caiannello/Pugputer6309/3D_Models/backplane_bot.png

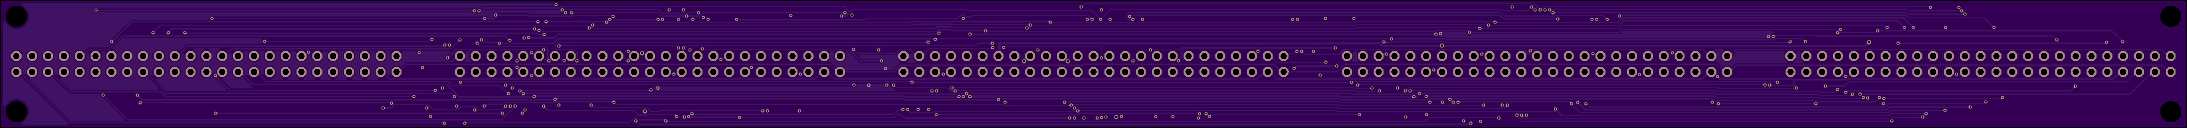
3D_Models/backplane_bot.png
