caiannello/Pugputer6309/3D_Models/backplane_top.png

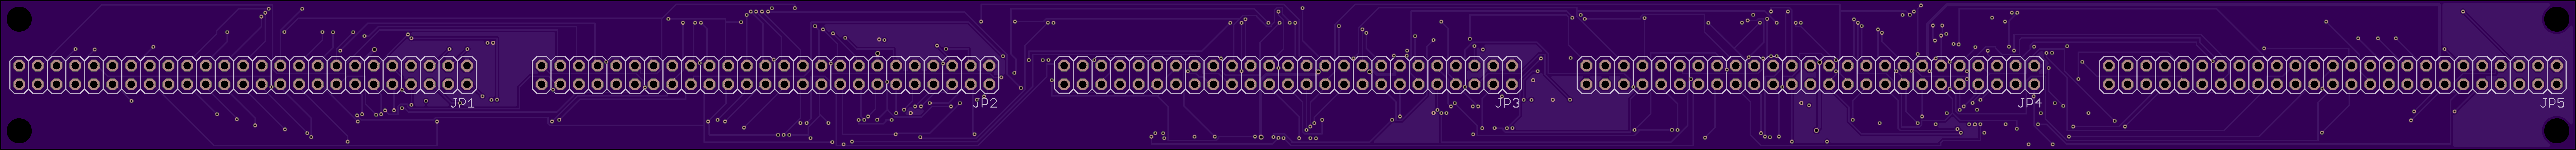
3D_Models/backplane_top.png
