caiannello/Pugputer6309/3D_Models/c_cpu_bot.png

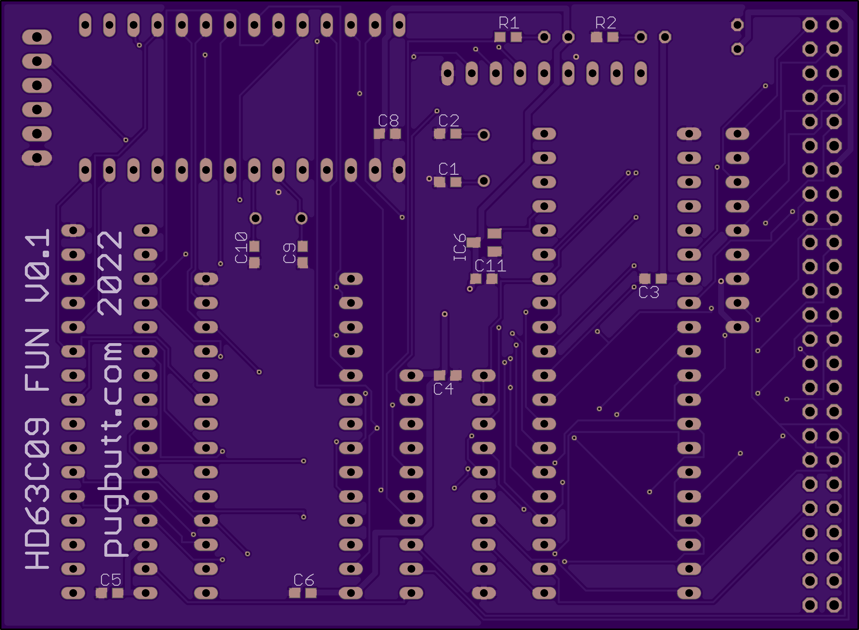
3D_Models/c_cpu_bot.png
