caiannello/Pugputer6309/3D_Models/c_cpu_top.png

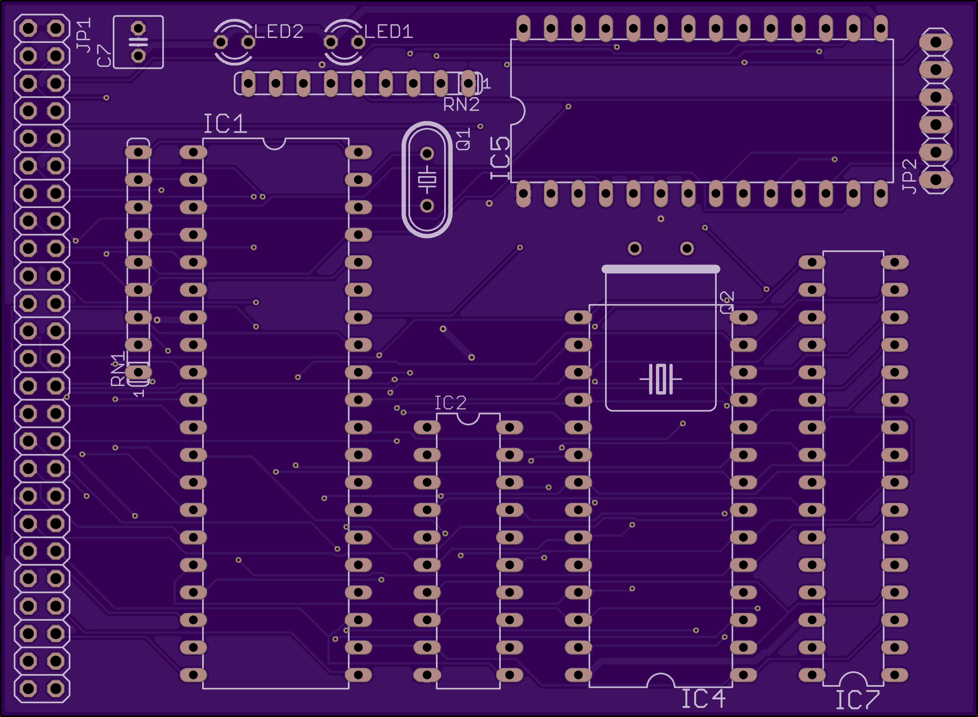
3D_Models/c_cpu_top.png
