caiannello/Pugputer6309/3D_Models/kb.jpg

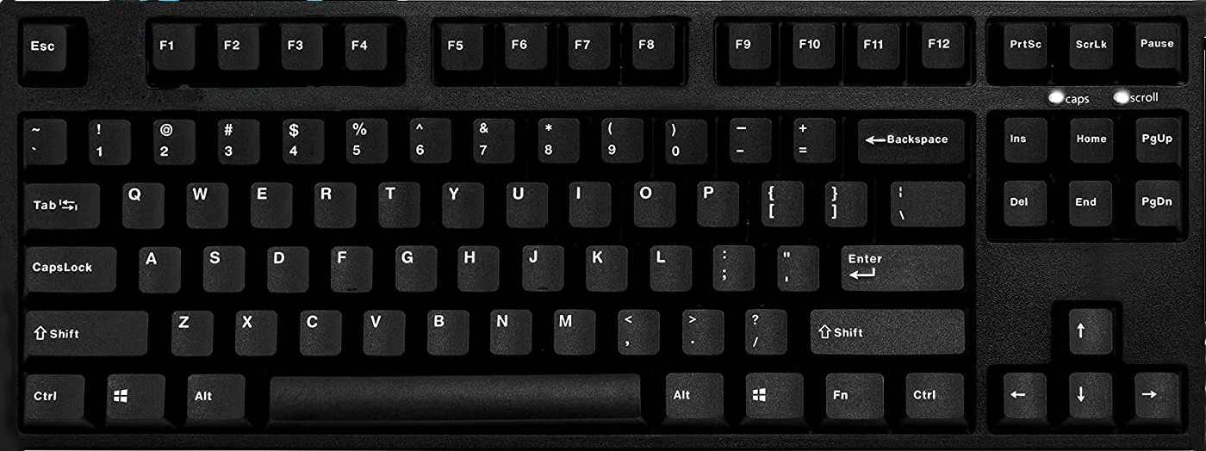
3D_Models/kb.jpg
