caiannello/Pugputer6309/3D_Models/lv_parallel_bot.png

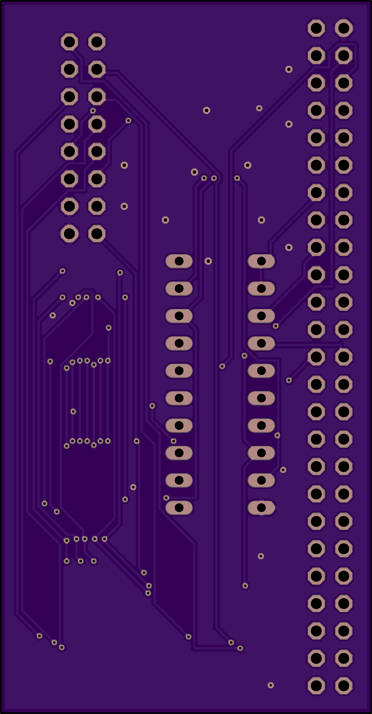
3D_Models/lv_parallel_bot.png
