caiannello/Pugputer6309/3D_Models/lv_parallel_top.png

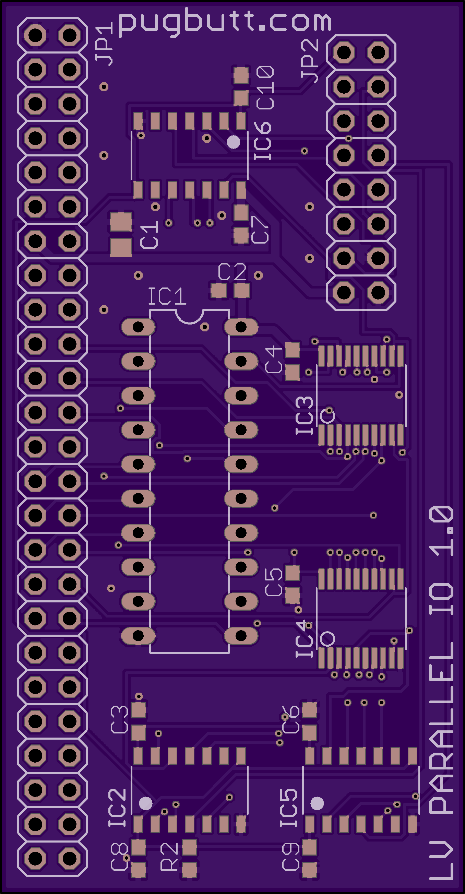
3D_Models/lv_parallel_top.png
