caiannello/Pugputer6309/3D_Models/mega_multi_bot.png

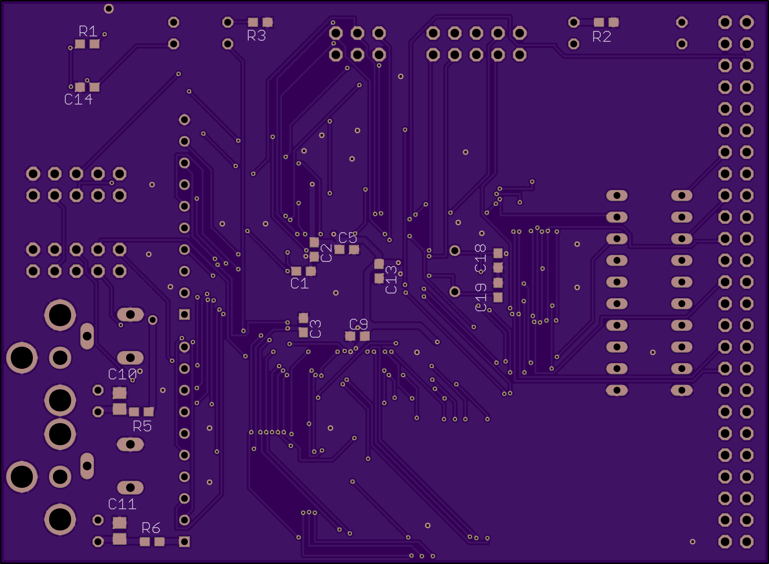
3D_Models/mega_multi_bot.png
