caiannello/Pugputer6309/3D_Models/mega_multi_top.png

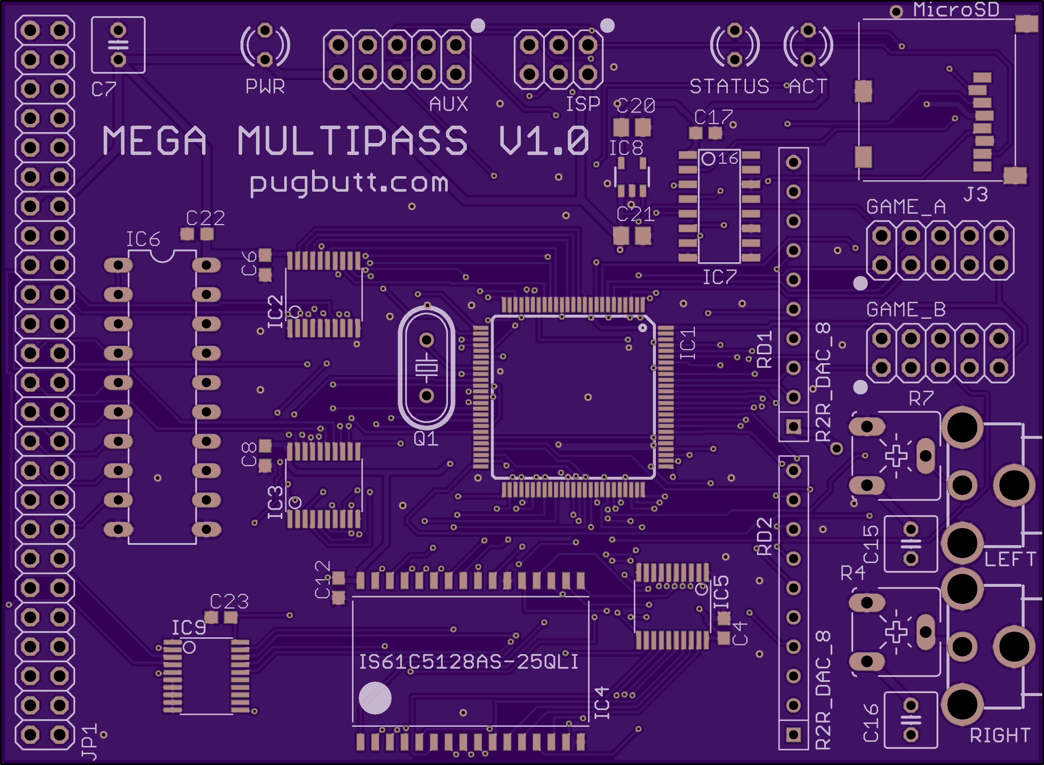
3D_Models/mega_multi_top.png
