caiannello/Pugputer6309/3D_Models/v9958_video_top.png

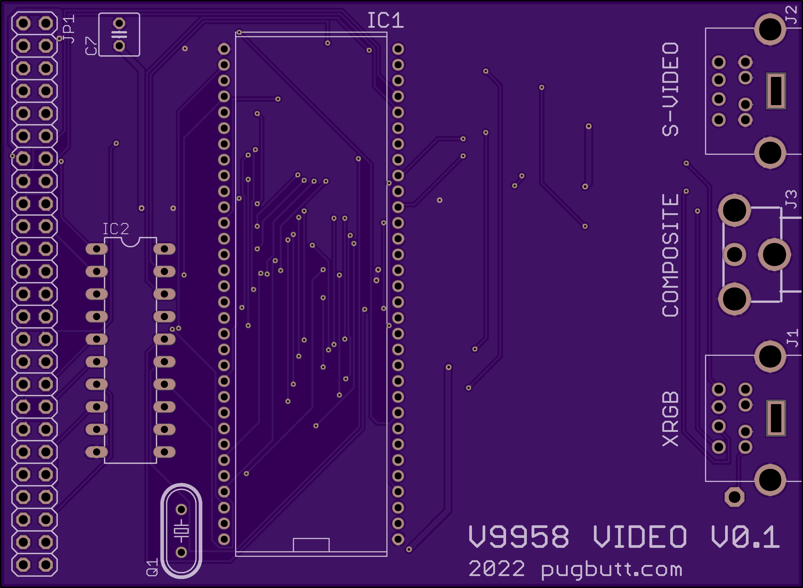
3D_Models/v9958_video_top.png
