caiannello/Pugputer6309/3D_Models/wedge_kb_top.png

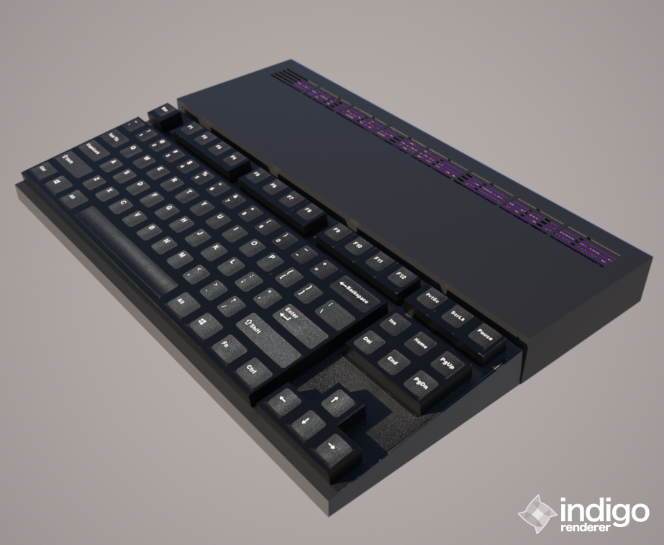
3D_Models/wedge_kb_top.png
