caiannello/Pugputer6309/Hardware/Bus Breakout Card/Layout.png

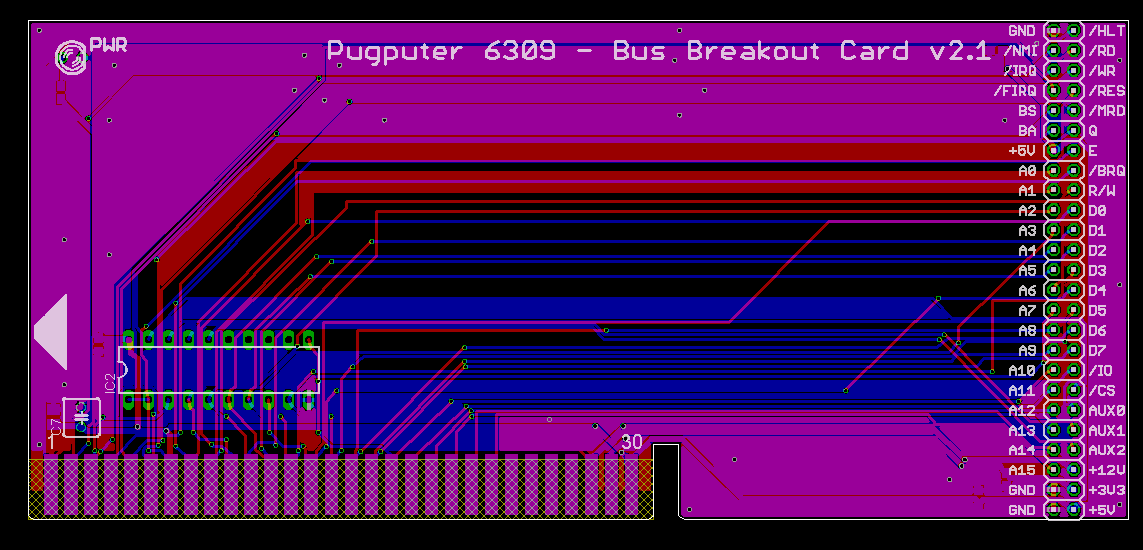
Hardware/Bus Breakout Card/Layout.png
