caiannello/Pugputer6309/Hardware/Bus Breakout Card/Schematic.png

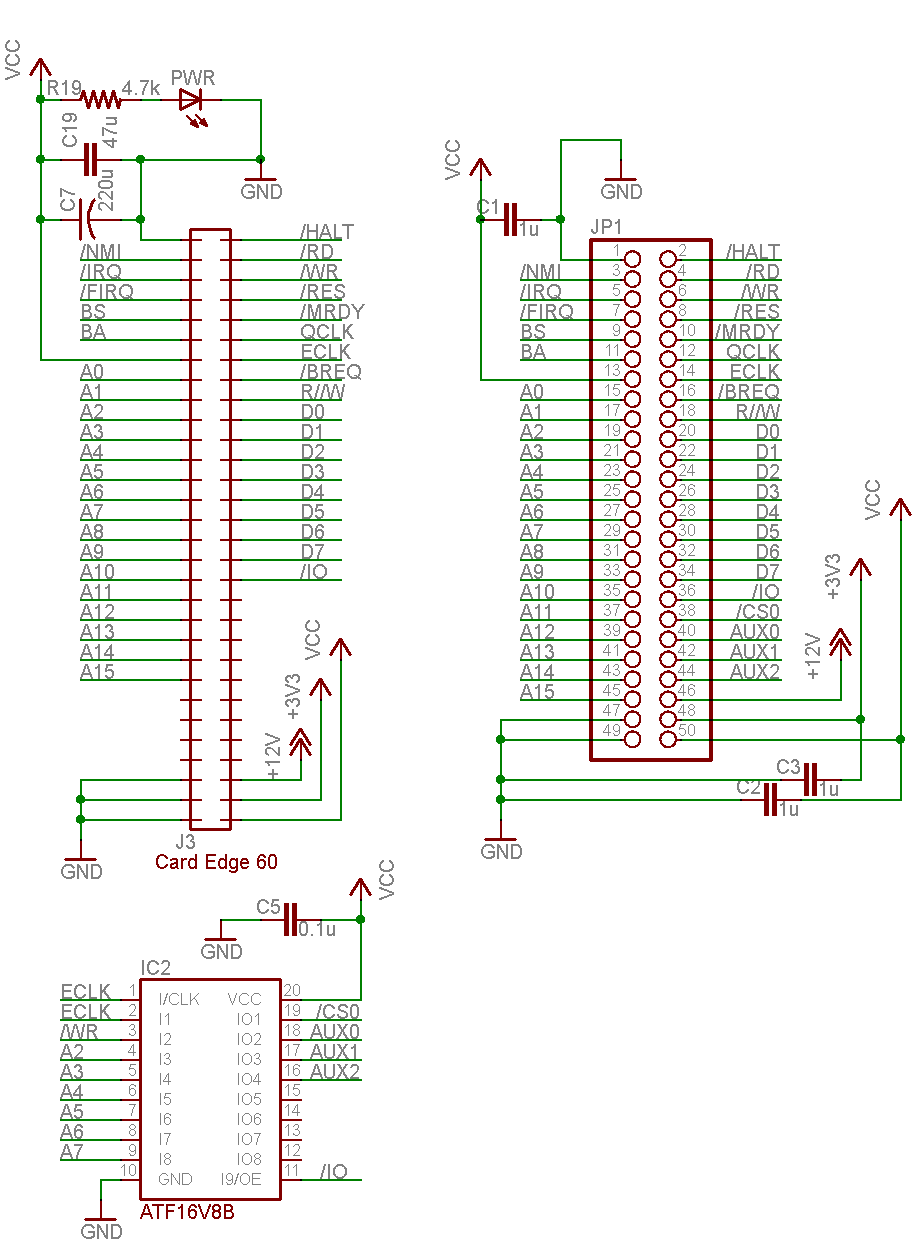
Hardware/Bus Breakout Card/Schematic.png
