caiannello/Pugputer6309/Hardware/Parallel IO Card/Parallel IO Card Schematic.png

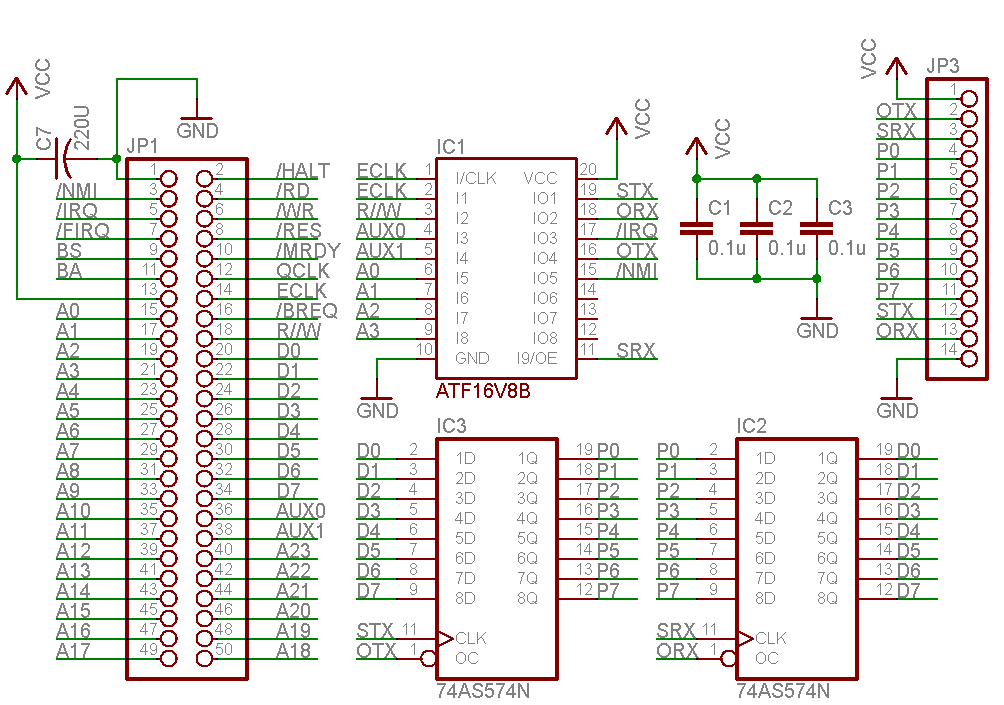
Hardware/Parallel IO Card/Parallel IO Card Schematic.png
