caiannello/Pugputer6309/Hardware/Pico_WLAN_SD_USB_RTC_AUDIO/layout.png

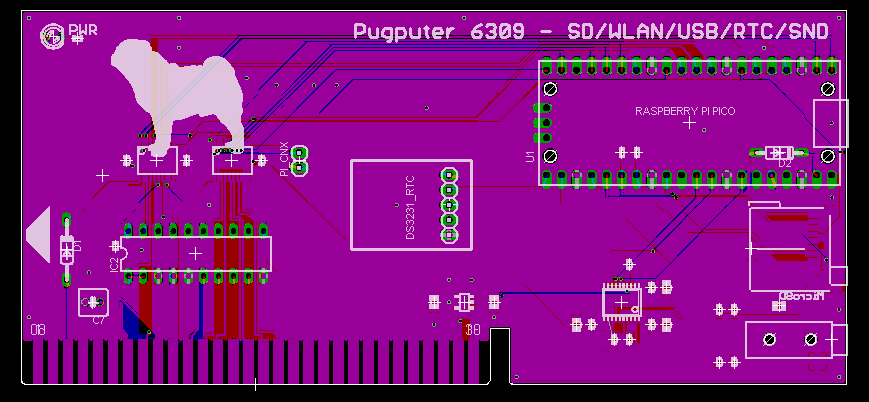
Hardware/Pico_WLAN_SD_USB_RTC_AUDIO/layout.png
