caiannello/Pugputer6309/Hardware/V9958 Video Card/past_revs/V9958 Video Card Schematic.png

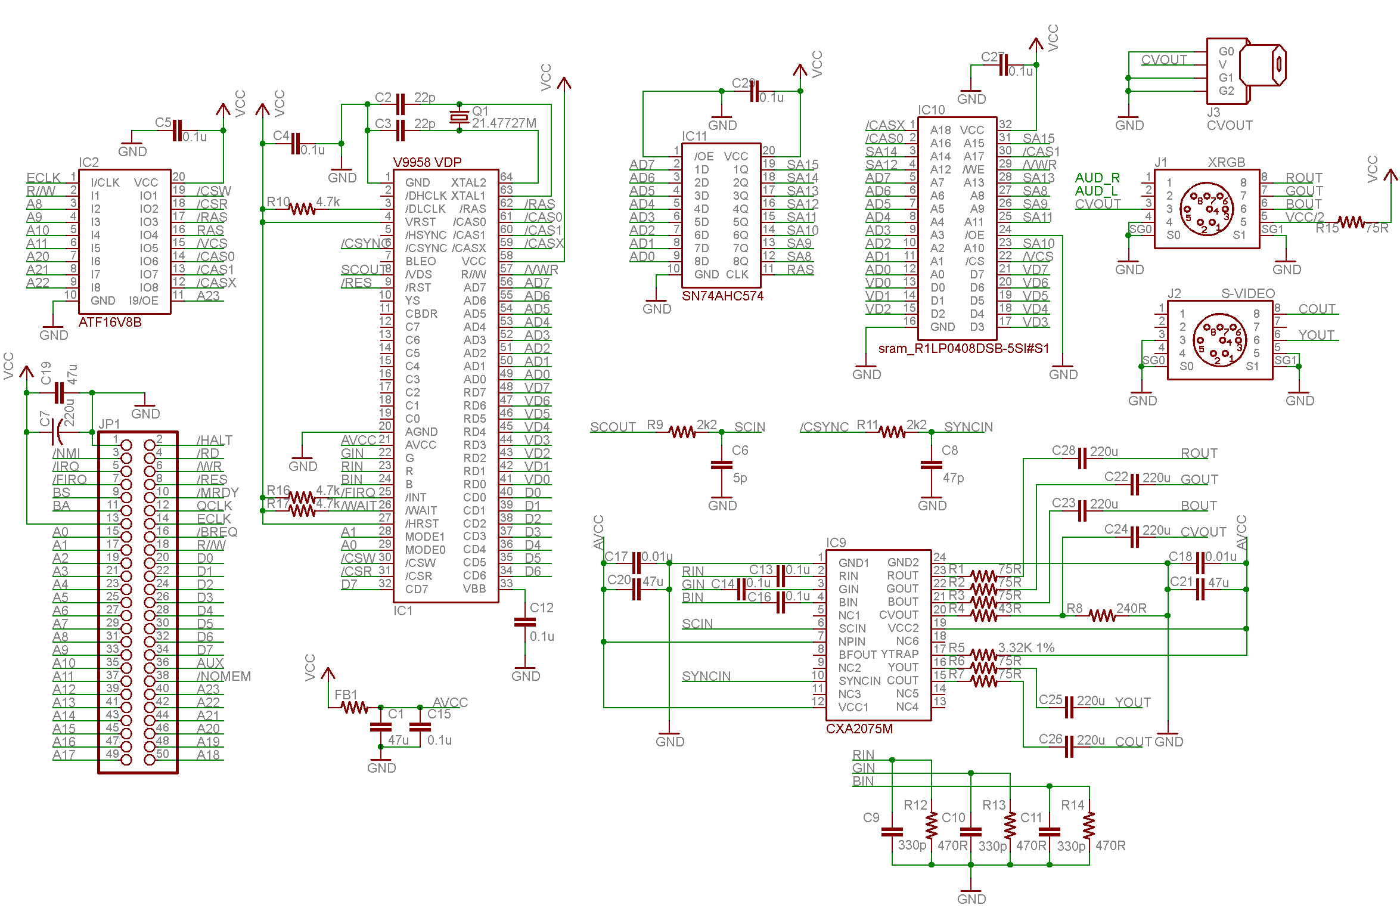
Hardware/V9958 Video Card/past_revs/V9958 Video Card Schematic.png
