caiannello/Pugputer6309/Software/dev_utils/font_palette.png

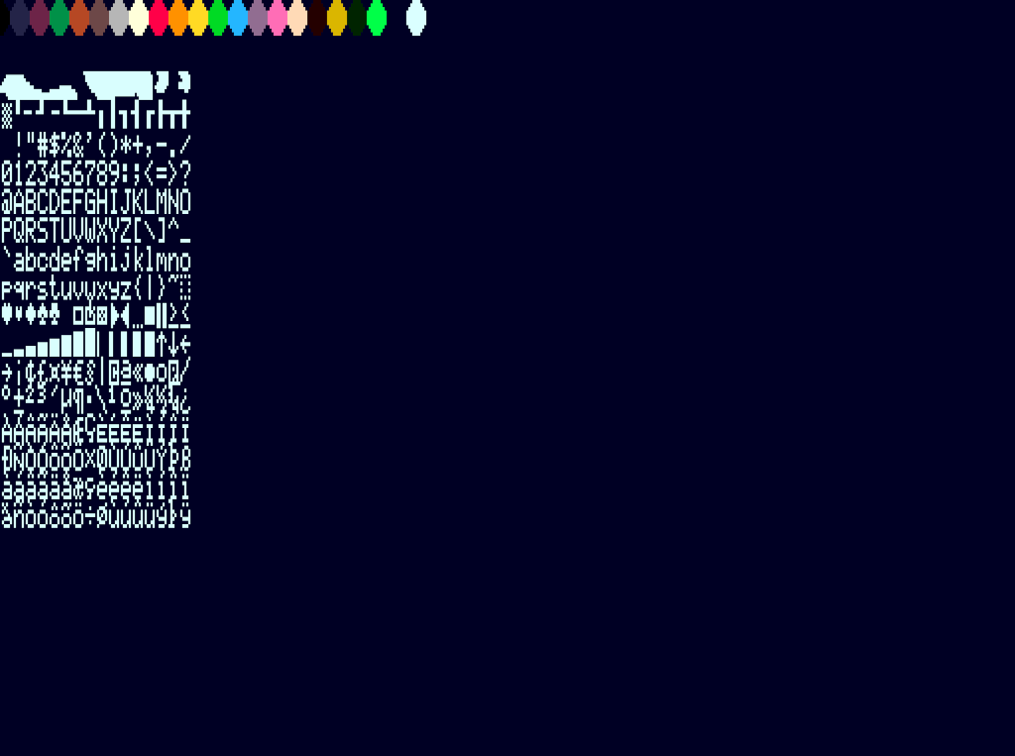
Software/dev_utils/font_palette.png
