caiannello/Pugputer6309/Software/dev_utils/font_palette/24bit_parrot.png

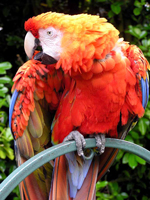
Software/dev_utils/font_palette/24bit_parrot.png
