caiannello/Pugputer6309/Hardware/6309 CPU Card/experimental/README.md

## 6309 CPU Card v2 through-hole experiment
```
Same as the Rev v2 in the parent directory, except most IC's are using
through-hole packages. (Had to give up one of the 512KB SRAM's to make room.)
```
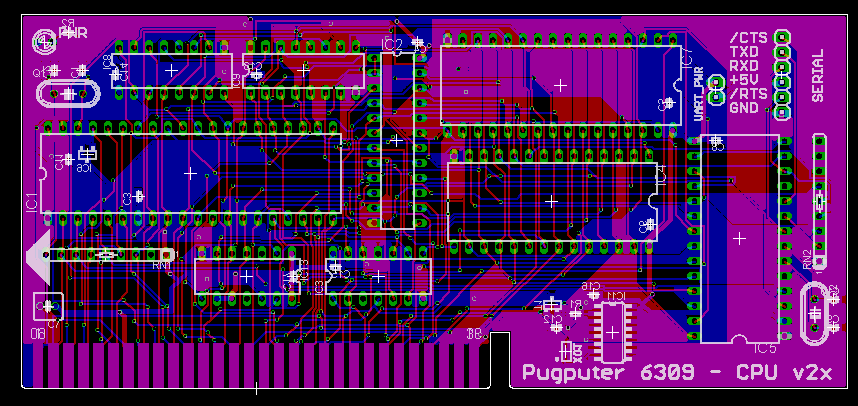
[picture p64: Hardware/6309 CPU Card/experimental/layout.png]
layout


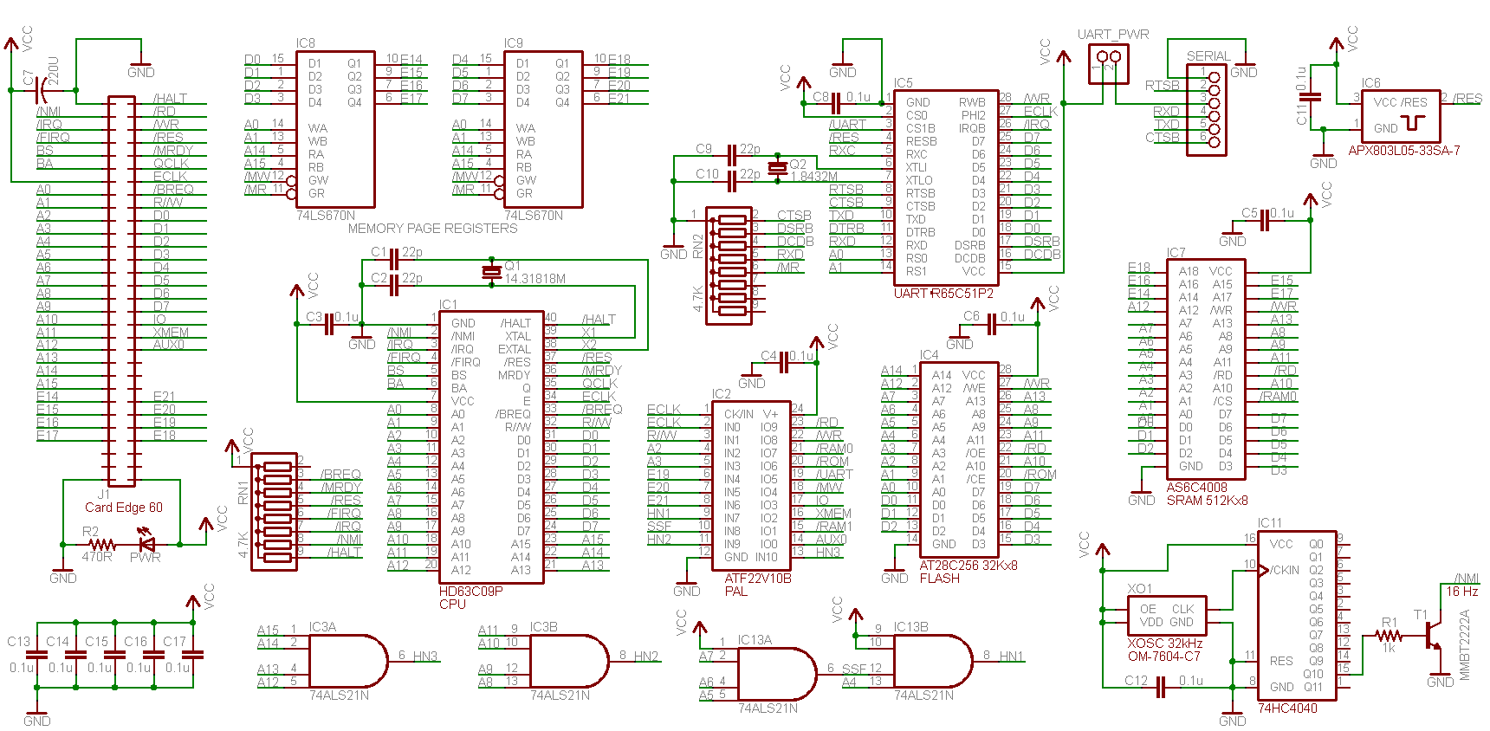
[picture p65: Hardware/6309 CPU Card/experimental/schematic.png]
schematic
