caiannello/Pugputer6309/Software/Arduino UNO/parallel_sd_audio/sd.h

///////////////////////////////////////////////////////////////////////////////
///////////////////////////////////////////////////////////////////////////////
#ifndef __SD_H__
#define __SD_H__

void sd_init(void);
void sd_service(void);

void sd_send_dir(uint8_t *path = NULL);
void sd_send_file(char * filepath);

#endif
///////////////////////////////////////////////////////////////////////////////
///////////////////////////////////////////////////////////////////////////////
