caiannello/Pugputer6309/Software/Teensy 4.1/multipass/audio.h

// ----------------------------------------------------------------------------
// ----------------------------------------------------------------------------
#ifndef __AUDIO_H__
#define __AUDIO_H__
// ----------------------------------------------------------------------------
#include <Audio.h>
// ----------------------------------------------------------------------------
#include "chords.h"
// ----------------------------------------------------------------------------
void aud_init();
void aud_service(void);
// ----------------------------------------------------------------------------
#endif
// ----------------------------------------------------------------------------
// ----------------------------------------------------------------------------
